studygeorge/givanta-binstack/docs/drawings/wall-section.png

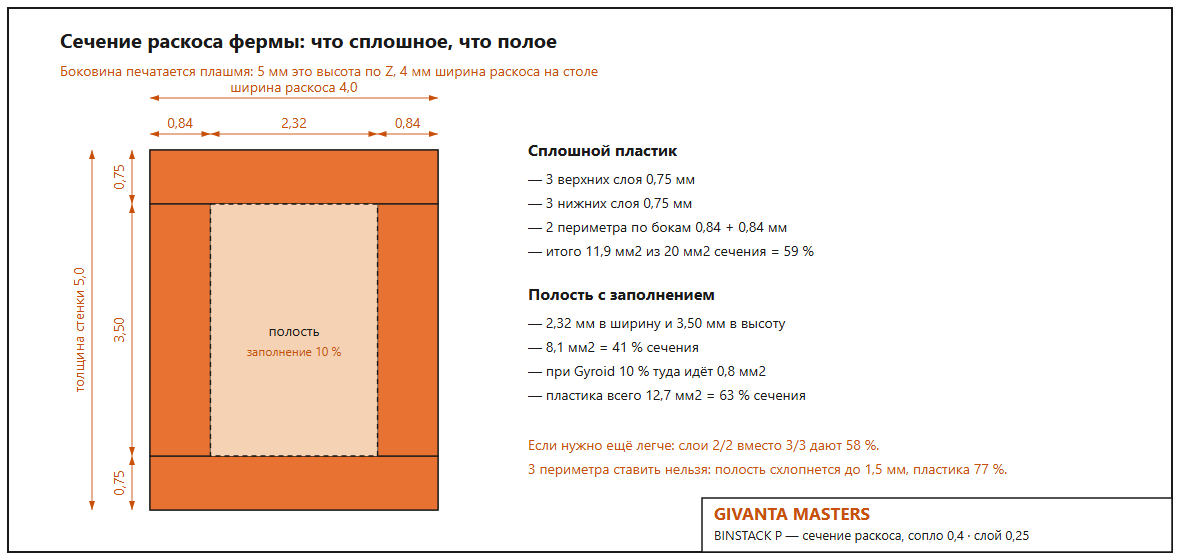
docs/drawings/wall-section.png
