studygeorge/givanta-binstack/renders/print-top.png

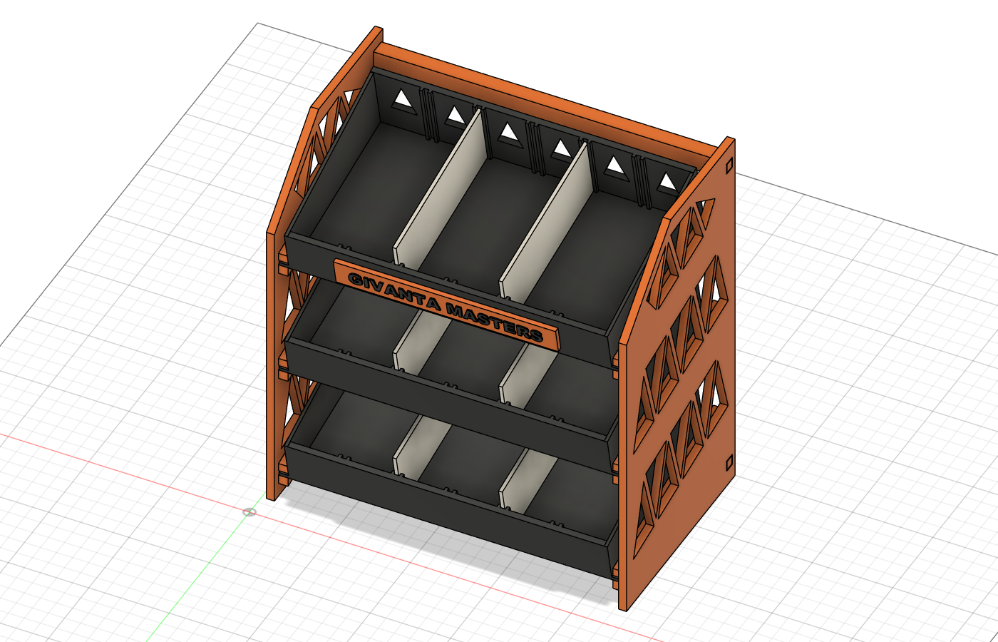
renders/print-top.png
